paula-delrio-arteaga/Fabacademy---3/pcb-photobioreactor/Photobioreactor_HOLES.png

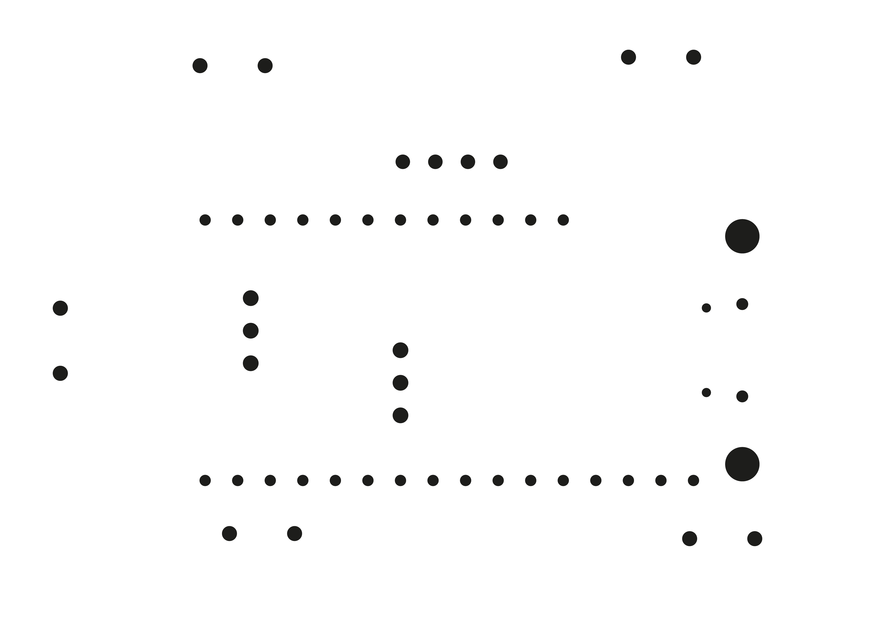
pcb-photobioreactor/Photobioreactor_HOLES.png
